ef15c/PS2_to_USB_converter/stm103_ps2_to_usb/tools/qipressportable_password0000/user/QiPress.ini

; QiPress Portable Ini File - Do Not Modify Manually
; Aalap Shah (http://aalapshah.in/qipress)
;
[app]
audioalert=0
autowordsensetime=999
bartimerreset=1
build=6
commandpromptpaste=0
dsblmousetyping=0
dsblmousetypingmsec=500
ecotimer=Shutdown•From Now•20210223010000
firstrundt=20210223
holdsensetime=200
keyconcat=+
keystkdisplaytype=0
lastabtdlgtab=5
laststngdlgsel=1•1
licagracceptdt=20210223
mousewraphor=0
mousewrapver=0
multiclksensetime=200
odometer=1463
plainpaste=0
qiffeine=0•10•LShift
recover=0
scribblepen=3•FFFFFF•255¦3•FF0000•221¦3•FFA500•187¦5•FFFF00•153¦2•008000•187¦3•0000FF•221¦4•4B0082•255¦5•EE82EE•153
scribblepennum=2
themenum=1
tooltipclass=tooltips_class32¦OfficeTooltip¦PSToolTip¦QToolTip
traytip=1
traytogglesicons=1
tripmeter=1463
typewriter=0
version=1.076
[cursorhalo]
colordiameter=50
colorfill=FF0080
colortransparency=48
colortype=0
crossfill=C0C0C0
crossisland=16
crossthickness=1
crosstransparency=255
enabled=0
spotfill=000000
spotlength=80
spottransparency=127
spottype=0
type=2
[cursortip]
bgcolor=FAFAFA
coordenable=1
enabled=0
fgcolor=4F4F4F
magnify=0
magnifypct=200
magnifysize=1
pxlcmyk=0
pxlhex=1
pxlhsl=0
pxlhsv=0
pxlrgb=1
txt=""
txtenable=0
txtfgcolor=000000
xoffset=16
yoffset=-16
[keyrenamebase]
enabled=0
[keyrenamecombi]
enabled=0
[keysets]
altgr=0
bkspcdelesc=0
capslockdisable=0
cursorctrl=1
enterspctab=1
functions=1
handedmodifiers=0
joystick=0
misc=1
modifiers=1
mouse=1
multimedia=0
numlockdisable=0
numpad=1
numpadstd=0
scrolllockdisable=0
standard=100
toggles=1
volume=0
[logobug]
clickthrough=1
enabled=0
imgfile=defaultlogo.png
mirrorhor=0
mirrorver=0
monitornum=1
rotatedeg=0
scaleimgpct=100
scalemon=0
scalemonpct=4
transparency=255
xposcenter=0
xposoffset=1•0•30
xposratio=0•9•1
yposcenter=0
yposoffset=1•1•30
yposratio=0•1•9
[osd]
bartime=1
bartimefmt=ddd, dd MMM yyyy, h:mm tt
bartimer=0000000
bartoggles=1
bartooltip=0
bartooltipcolor=FFFFFF
bartooltiplabel=ToolTip:
barvol=1
barvolbgcolor=000000
barvolfgcolor=FF0080
barvoltxcolor=FFFFFF
bgfillcolor=000000
bgimgfile=defaultbg.jpg
bgnullcolor=000000
bgopt=0
centertext=0
clickthrough=1
cornerradius=10
countrepeat=1
detecthold=0
dimkeyup=0
displaydur=2000
enabled=1
engkeynames=0
fadein=0
fadeout=300
fontcolor=FFFFFF
fontsize=16
fontsmalltobigpct=55
fontstyle=Arial
ignoresinglelbutton=0
kbdlayout=eng-US
keyhistory=3
keyhistorycolor=FFFFFF
keyhistorydur=Auto
keyhistoryenabled=1
livekeydur=Auto
livekeys=1
livekeysonlytopbar=0
maxchars=19
monitornum=1
nudge=1
rtl=0
shadowtext=0
sm3widthfactor=0
statictext=10100nounours{;}ONYX
statictextcolor=FFFFFF
statictextfontsize=9
statictextrotateminutes=3
textsymbols=0
transparency=170
uppercaseaz=1
width=200
widthforce=0
wincapdetectable=0
xposcenter=0
xposoffset=1•1•10
xposratio=0•1•1
yposcenter=0
yposoffset=1•0•40
yposratio=0•7•1
[qilaunchr]
aottoggle=1100•Space•0
apptoggle=1000•Esc•0
cursorcoord=0001•c•1
cursorcopycol=0001•p•1
cursorhalo=0001•h•1
disablesec=8
force=0
hibernate=1100•BackSpace•1
logoff=0000•None•0
magnify=1100•m•1
osdtoggle=1000•Del•1
powerdown=1100•Del•1
qiffeine=0000•None•0
qimeter=0000•None•0
restart=0000•None•0
scribble=1001•s•0
shutdown=1100•Del•0
sleep=1100•BackSpace•0
timeddisable=1000•BackSpace•1
vismouse=0001•v•0
[visualmouse]
enabled=0
iconcolor=C0C0C0
iconsize=1
lbutcolor=FF0000
lingerdur=0
mbutcolor=00FF00
opacity=221
posfixed=0
rbutcolor=0000FF
ringthick=5
type=0
wheelcolor=FF0080
xbut1color=FF0000
xbut2color=0000FF
